nealey/uilleann/daye/chanter/chanter-bottom.scad

include <../common.scad>
use <./chanter.scad>

tenon(top=false) {
  chanter();
}
