nealey/uilleann/daye/chanter/chanter-top.scad

use <./chanter.scad>

tenon(top=true) {
  chanter();
}
