nealey/uilleann/daye/drones/baritone/tuner-barrel.scad

use <assembly.scad>

drone_baritone_tuner_barrel();
