nealey/uilleann/daye/drones/baritone/tuner-end.scad

use <assembly.scad>

drone_baritone_tuner_end();
