nealey/uilleann/daye/drones/tenor/tuner-barrel.scad

include <assembly.scad>

drone_tenor_tuner_barrel();
