nealey/uilleann/daye/drones/tenor/tuner-end.scad

include <assembly.scad>

drone_tenor_tuner_end();
